Landerson65/EnginHears/Deliverable_Software/FFT_IFFT/FFT_IFFT.c

/* Factored discrete Fourier transform, or FFT, and its inverse iFFT */

#include <assert.h>
#include <math.h>
#include <stdio.h>
#include <stdlib.h>


#define q	3		/* for 2^3 points */
#define N	(1<<q)		/* N-point FFT, iFFT */

typedef float real;
typedef struct { real Re; real Im; } complex;

#ifndef PI
# define PI	3.14159265358979323846264338327950288
#endif

/* Print a vector of complexes as ordered pairs. */
static void print_vector(const char* title, complex* x, int n)
{
	int i;
	printf("%s (dim=%d):", title, n);
	for (i = 0; i < n; i++) printf(" %5.2f,%5.2f ", x[i].Re, x[i].Im);
	putchar('\n');
	return;
}
/*
   fft(v,N):
   [0] If N==1 then return.
   [1] For k = 0 to N/2-1, let ve[k] = v[2*k]
   [2] Compute fft(ve, N/2);
   [3] For k = 0 to N/2-1, let vo[k] = v[2*k+1]
   [4] Compute fft(vo, N/2);
   [5] For m = 0 to N/2-1, do [6] through [9]
   [6]   Let w.re = cos(2*PI*m/N)
   [7]   Let w.im = -sin(2*PI*m/N)
   [8]   Let v[m] = ve[m] + w*vo[m]
   [9]   Let v[m+N/2] = ve[m] - w*vo[m]
 */

void fft(complex* v, int n, complex* tmp)
{
	if (n > 1) {			/* otherwise, do nothing and return */
		int k, m;    complex z, w, * vo, * ve;
		ve = tmp; vo = tmp + n / 2;
		for (k = 0; k < n / 2; k++) {
			ve[k] = v[2 * k];
			vo[k] = v[2 * k + 1];
		}
		fft(ve, n / 2, v);		/* FFT on even-indexed elements of v[] */
		fft(vo, n / 2, v);		/* FFT on odd-indexed elements of v[] */
		for (m = 0; m < n / 2; m++) {
			w.Re = cos(2 * PI * m / (double)n);
			w.Im = -sin(2 * PI * m / (double)n);
			z.Re = w.Re * vo[m].Re - w.Im * vo[m].Im;	/* Re(w*vo[m]) */
			z.Im = w.Re * vo[m].Im + w.Im * vo[m].Re;	/* Im(w*vo[m]) */
			v[m].Re = ve[m].Re + z.Re;
			v[m].Im = ve[m].Im + z.Im;
			v[m + n / 2].Re = ve[m].Re - z.Re;
			v[m + n / 2].Im = ve[m].Im - z.Im;
		}
	}
	return;
}

/*
   ifft(v,N):
   [0] If N==1 then return.
   [1] For k = 0 to N/2-1, let ve[k] = v[2*k]
   [2] Compute ifft(ve, N/2);
   [3] For k = 0 to N/2-1, let vo[k] = v[2*k+1]
   [4] Compute ifft(vo, N/2);
   [5] For m = 0 to N/2-1, do [6] through [9]
   [6]   Let w.re = cos(2*PI*m/N)
   [7]   Let w.im = sin(2*PI*m/N)
   [8]   Let v[m] = ve[m] + w*vo[m]
   [9]   Let v[m+N/2] = ve[m] - w*vo[m]
 */

void ifft(complex* v, int n, complex* tmp)
{
	if (n > 1) {			/* otherwise, do nothing and return */
		int k, m;    complex z, w, * vo, * ve;
		ve = tmp; vo = tmp + n / 2;
		for (k = 0; k < n / 2; k++) {
			ve[k] = v[2 * k];
			vo[k] = v[2 * k + 1];
		}
		ifft(ve, n / 2, v);		/* FFT on even-indexed elements of v[] */
		ifft(vo, n / 2, v);		/* FFT on odd-indexed elements of v[] */
		for (m = 0; m < n / 2; m++) {
			w.Re = cos(2 * PI * m / (double)n);
			w.Im = sin(2 * PI * m / (double)n);
			z.Re = w.Re * vo[m].Re - w.Im * vo[m].Im;	/* Re(w*vo[m]) */
			z.Im = w.Re * vo[m].Im + w.Im * vo[m].Re;	/* Im(w*vo[m]) */
			v[m].Re = ve[m].Re / 2 + z.Re / 2;
			v[m].Im = ve[m].Im / 2 + z.Im / 2;
			v[m + n / 2].Re = ve[m].Re / 2 - z.Re / 2;
			v[m + n / 2].Im = ve[m].Im / 2 - z.Im / 2;
		}
	}
	return;
}

void gainCalculation( double* gainArray, double g, double fs, double first, double second, double third, double fourth) {
	int k = 0;
	double T = 1 / fs;
	double firstC;
	double secondC;
	double secondC2;
	double thirdC;
	double thirdC2;
	double fifthC;
	double fifthC2;
	double kk = 0.0;

	firstC = 0.3 * (g - 1.0) / first;
	while ((kk / N) <= (first / fs)) {
		double val = firstC * kk / (N * T) + 1;
		//printf(" %5.2f", val);
		gainArray[k] = firstC * kk / (N * T) + 1;
		gainArray[N - k - 1] = gainArray[k];
		kk = kk + 1.0;
		k = k + 1;
	}
	//Sets the gain for the second stage of frequencies
	secondC = firstC * first + 1;
	secondC2 = (second - first) / 5;
	while ((kk / N) <= (second / fs)) {
		gainArray[k] = 1 + (secondC - 1) * exp(-((kk / (N * T)) - first) / secondC2);
		gainArray[N - k - 1] = gainArray[k];
		k = k + 1;
		kk = kk + 1;
	}

	///Sets the gain for the third stage of frequencies
	thirdC = 1 + (secondC - 1) * exp(-second / secondC2);
	thirdC2 = (third - second) / 5;
	while ((kk / N) <= (third / fs)) {
		gainArray[k] = g + (thirdC - g) * exp(-((kk / (N * T) - second)) / thirdC2);
		gainArray[N - k - 1] = gainArray[k];
		k = k + 1;
		kk = kk + 1;
	}

	//Sets the gain for the fourth stage of frequencies
	while ((kk / N) <= (fourth / fs)) {
		gainArray[k] = g;
		gainArray[N - k - 1] = gainArray[k];
		k = k + 1;
		kk = kk + 1;
	}

	//Sets the gain for the fifth stage of frequencies
	fifthC = g;
	fifthC2 = (fs / 2 - fourth) / 5;
	while ((kk / N) <= .5) {
		gainArray[k] = 1 + (fifthC - 1) * exp(-((kk / (N * T)) - fourth) / fifthC2);
		gainArray[N - k - 1] = gainArray[k];
		k = k + 1;
		kk = kk + 1;
	}
}

void apply_gain(complex* x, double* gainArray, int n)
{
	int i;
	printf("%s (dim=%d):", "Gain Added", n);
	for (i = 0; i < n; i++) {
		x[i].Re = x[i].Re * gainArray[i];
		x[i].Im = x[i].Im * gainArray[i];

		printf(" %5.2f,%5.2f ", x[i].Re, x[i].Im);
	}
	putchar('\n');
	return;
}


int main(void)
{
	complex v[N], v1[N], scratch[N];
	double gainArray[N];
	double first = 1000.0;
	double second = 1500.0;
	double third = 2550.0;
	double fourth = 5000.0;
	double maxGain = 5.0;
	double fs = 25000.0;
	int k;

	/* Fill v[] with a function of known FFT: */
	for (k = 0; k < N; k++) {
		v[k].Re = 0.125 * cos(2 * PI * k / (double)N);
		v[k].Im = 0.125 * sin(2 * PI * k / (double)N);
		v1[k].Re = 0.3 * cos(2 * PI * k / (double)N);
		v1[k].Im = -0.3 * sin(2 * PI * k / (double)N);
	}
	/* Apply the gain */
	gainCalculation(gainArray, maxGain, fs, first, second, third, fourth);

	/* Print out gain array*/
	/*
	printf("%s (dim=%d):", "Gain", N);
	for (int i = 0; i < N; i++) {
		printf(" %5.2f", gainArray[i]);
	}
	*/

	/* FFT, iFFT of v[]: */
	print_vector("Orig", v, N);
	fft(v, N, scratch);
	print_vector(" FFT", v, N);
	ifft(v, N, scratch);
	print_vector("iFFT", v, N);
	putchar('\n');
	putchar('\n');

	/* FFT, applied gain, iFFT of v[]: */
	print_vector("Orig", v, N);
	fft(v, N, scratch);
	print_vector(" FFT", v, N);
	apply_gain(v, gainArray, N);
	ifft(v, N, scratch);
	print_vector("iFFT", v, N);
	putchar('\n');
	putchar('\n');

	exit(EXIT_SUCCESS);
}
