Landerson65/EnginHears/Deliverable_Software/FFT_IFFT/assert.h

/* assert.h
Copyright (C) 2001, 2003 Free Software Foundation, Inc.
Written by Stephane Carrez (stcarrez@nerim.fr)       

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
In addition to the permissions in the GNU General Public License, the
Free Software Foundation gives you unlimited permission to link the
compiled version of this file with other programs, and to distribute
those programs without any restriction coming from the use of this
file.  (The General Public License restrictions do apply in other
respects; for example, they cover modification of the file, and
distribution when not linked into another program.)

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
You should have received a copy of the GNU General Public License
along with this program; see the file COPYING.  If not, write to
the Free Software Foundation, 59 Temple Place - Suite 330,
Boston, MA 02111-1307, USA.  */

#ifndef _ASSERT_H
#define _ASSERT_H

#ifdef NDEBUG
# define assert(EX)
#else
# define assert(EX) (void)((EX) || (__assert (#EX, __FILE__, __LINE__),0))
#endif

#ifdef __cplusplus
extern "C" {
#endif

extern void __assert (const char *msg, const char *file, int line);

#ifdef __cplusplus
};
#endif
#endif
